bbakersmith/hl3-headwater/src/headwater_state.c

#include "stdint.h"
#include <stdio.h>

#include "headwater_state.h"

void headwater_state_update_samples_per_beat(
  HeadwaterStateChannel *channel,
  uint16_t samples_per_beat
) {
  if(channel->multiplier == 0)
    return;

  uint8_t multiplier = channel->multiplier;
  uint16_t base_samples = samples_per_beat / multiplier;
  uint8_t remainder = samples_per_beat % multiplier;
  uint16_t multiplier_100 = multiplier * 100;

  uint16_t no_remainder_frequency;
  uint16_t remainder_frequency;
  if(remainder != 0) {
    no_remainder_frequency = multiplier_100 / (multiplier - remainder);
    remainder_frequency = multiplier_100 / remainder;
  } else {
    no_remainder_frequency = 0;
    remainder_frequency = 1;
  }

  channel->samples_per_beat = base_samples;
  channel->samples_per_beat_with_remainder = base_samples;

  channel->remainder_frequency = remainder_frequency;
  channel->remainder_priority = remainder_frequency;

  channel->no_remainder_frequency = no_remainder_frequency;
  channel->no_remainder_priority = no_remainder_frequency;
}

HeadwaterStateChannel headwater_state_channel_new(uint16_t samples_per_beat) {
  HeadwaterStateChannel channel = {
    .samples = 0,
    .beats = 0,
    .multiplier = 1,
    .output = 0
  };
  headwater_state_update_samples_per_beat(&channel, samples_per_beat);
  return channel;
}

HeadwaterState headwater_state_new(void) {
  uint32_t samples_per_second = 1000;

  uint16_t samples_per_beat = headwater_state_bpm_to_samples(
    samples_per_second,
    HEADWATER_STATE_DEFAULT_BPM
  );

  HeadwaterStateChannel bpm_channel =
    headwater_state_channel_new(samples_per_beat);

  HeadwaterStateChannel multiplier_a_channel =
    headwater_state_channel_new(samples_per_beat);

  HeadwaterStateChannel multiplier_b_channel =
    headwater_state_channel_new(samples_per_beat);

  HeadwaterStateChannel midi_channel =
    headwater_state_channel_new(samples_per_beat);

  midi_channel.multiplier = 24;
  headwater_state_update_samples_per_beat(&midi_channel, samples_per_beat);

  HeadwaterState state = {
    .bpm = HEADWATER_STATE_DEFAULT_BPM,
    .bpm_channel = bpm_channel,
    .mode = HEADWATER_STATE_MODE_INTERNAL,
    .multiplier_a_channel = multiplier_a_channel,
    .multiplier_b_channel = multiplier_b_channel,
    .midi_channel = midi_channel,
    .output_enabled = 0,
    .preset = 0,
    .reset_count = 0,
    .samples_per_second = samples_per_second,
    .samples_since_reset_count = 0
  };
  return state;
}

uint16_t headwater_state_samples_to_bpm(
  uint32_t samples_per_second,
  uint16_t samples_per_beat
) {
  return (samples_per_second * SECONDS_IN_MINUTE * 10) / samples_per_beat;
}

uint16_t headwater_state_bpm_to_samples(
  uint32_t samples_per_second,
  uint16_t bpm
) {
  return (samples_per_second * SECONDS_IN_MINUTE * 10) / bpm;
}

void headwater_state_stop(HeadwaterState *state) {
  state->output_enabled = 0;
  state->reset_count = 0;
  (state->midi)->writer(MIDI_STOP);
}

void headwater_state_reset_channel(HeadwaterStateChannel *channel) {
  channel->beats = 0;
  channel->samples = 0;
  channel->samples_per_beat_with_remainder = channel->samples_per_beat;
}

void headwater_state_play(HeadwaterState *state) {
  uint8_t previous_output_enabled = state->output_enabled;

  headwater_state_reset_channel(&state->bpm_channel);
  headwater_state_reset_channel(&state->multiplier_a_channel);
  headwater_state_reset_channel(&state->multiplier_b_channel);
  headwater_state_reset_channel(&state->midi_channel);

  state->reset_count++;

  switch(state->mode) {
    case HEADWATER_STATE_MODE_EXTERNAL:
    case HEADWATER_STATE_MODE_TAP:
      if(state->reset_count == 1) {
        // TODO display unknown ---.- ???.?
      } else {
        state->output_enabled = 1;

        state->bpm_channel.samples_per_beat =
          state->samples_since_reset_count;

        state->change_flags |= (1 << HEADWATER_STATE_CHANGE_BPM);
      }
      state->samples_since_reset_count = 0;
      break;
    default:
      state->output_enabled = 1;
      break;
  }

  if(state->output_enabled) {
    if(previous_output_enabled == 0) {
      (state->midi)->writer(MIDI_START);
    } else {
      (state->midi)->writer(MIDI_CONTINUE);
    }
  }
}

void headwater_state_channel_fire(
  HeadwaterStateChannel *channel
) {
  channel->samples_per_beat_with_remainder = channel->samples_per_beat;

  if(channel->remainder_priority < channel->no_remainder_priority) {
    channel->samples_per_beat_with_remainder++;
    channel->remainder_priority += channel->remainder_frequency;
  } else {
    channel->no_remainder_priority += channel->no_remainder_frequency;
  }

  // TODO prevent priority overflow (write test first)

  channel->beats++;
  channel->output = 1;
}

void headwater_state_channel_update_output(
  HeadwaterStateChannel *channel
) {
  if(
    channel->multiplier != 0
    && channel->beats < channel->multiplier
    && channel->samples == 0
  ) {
    headwater_state_channel_fire(channel);
  } else {
    channel->output = 0;
  }
}

void headwater_state_channel_reset(
  HeadwaterStateChannel *channel
) {
  channel->beats = 0;
  channel->samples = 0;
  channel->no_remainder_priority = channel->no_remainder_frequency;
  channel->remainder_priority = channel->remainder_frequency;
}

void headwater_state_update_outputs(HeadwaterState *state) {
  headwater_state_channel_update_output(&state->bpm_channel);

  if(state->bpm_channel.output == 1) {
    headwater_state_channel_reset(&state->multiplier_a_channel);
    headwater_state_channel_reset(&state->multiplier_b_channel);
    headwater_state_channel_reset(&state->midi_channel);
  }

  headwater_state_channel_update_output(&state->multiplier_a_channel);
  headwater_state_channel_update_output(&state->multiplier_b_channel);
  headwater_state_channel_update_output(&state->midi_channel);
}

void headwater_state_channel_increment_counts(
  HeadwaterStateChannel *channel
) {
  if(channel->samples < UINT16_MAX)
    channel->samples++;

  if(channel->beats < channel->multiplier) {
    if(channel->samples_per_beat_with_remainder <= channel->samples) {
      channel->samples = 0;
    }
  }
}

void headwater_state_increment_counts(HeadwaterState *state) {
  headwater_state_channel_increment_counts(&state->bpm_channel);
  headwater_state_channel_increment_counts(&state->multiplier_a_channel);
  headwater_state_channel_increment_counts(&state->multiplier_b_channel);
  headwater_state_channel_increment_counts(&state->midi_channel);

  // timeout & reset
  if(state->samples_since_reset_count < UINT16_MAX) {
    state->samples_since_reset_count++;
  } else {
    state->reset_count = 0;
    state->samples_since_reset_count = 0;
  }

  // loop based on internal clock for internal and tap modes
  switch(state->mode) {
    case HEADWATER_STATE_MODE_INTERNAL:
    case HEADWATER_STATE_MODE_TAP:
      state->bpm_channel.beats = 0;
      break;
    default:
      break;
  }
}

void headwater_state_cycle(HeadwaterState *state) {
  if(state->output_enabled == 1) {
    headwater_state_update_outputs(state);
  } else {
    state->bpm_channel.output = 0;
    state->multiplier_a_channel.output = 0;
    state->multiplier_b_channel.output = 0;
    state->midi_channel.output = 0;
  }

  if(state->bpm_channel.output == 1)
    headwater_state_handle_change_after_beat(state);

  headwater_state_increment_counts(state);
}

bool headwater_state_has_change_now(uint8_t change_flags) {
  uint8_t mask =
    (1 << HEADWATER_STATE_CHANGE_STOP)
    | (1 << HEADWATER_STATE_CHANGE_PLAY)
    | (1 << HEADWATER_STATE_CHANGE_MODE);

  return (mask & change_flags) != 0;
}

void headwater_state_handle_change_now(HeadwaterState *state) {
  uint8_t change_flags = state->change_flags;
  if(!headwater_state_has_change_now(change_flags))
    return;

  if((change_flags & (1 << HEADWATER_STATE_CHANGE_PLAY))) {
    state->change_flags &= ~(1 << HEADWATER_STATE_CHANGE_PLAY);
    headwater_state_play(state);

  } else if((change_flags & (1 << HEADWATER_STATE_CHANGE_STOP))) {
    state->change_flags &= ~(1 << HEADWATER_STATE_CHANGE_STOP);
    headwater_state_stop(state);

  } else if((change_flags & (1 << HEADWATER_STATE_CHANGE_MODE))) {
    state->change_flags &= ~(1 << HEADWATER_STATE_CHANGE_MODE);
    // react to mode change here, if ever a reason to
  }
}

bool headwater_state_has_change_after_beat(uint8_t change_flags) {
  uint8_t mask =
    (1 << HEADWATER_STATE_CHANGE_BPM)
    | (1 << HEADWATER_STATE_CHANGE_MULTIPLIER_A)
    | (1 << HEADWATER_STATE_CHANGE_MULTIPLIER_B);

  return (mask & change_flags) != 0;
}

void headwater_state_handle_change_after_beat(HeadwaterState *state) {
  uint8_t change_flags = state->change_flags;
  if(!headwater_state_has_change_after_beat(change_flags))
    return;

  if((change_flags & (1 << HEADWATER_STATE_CHANGE_BPM))) {
    state->change_flags &= ~(1 << HEADWATER_STATE_CHANGE_BPM);
    state->change_flags &= ~(1 << HEADWATER_STATE_CHANGE_MULTIPLIER_A);
    state->change_flags &= ~(1 << HEADWATER_STATE_CHANGE_MULTIPLIER_B);

    switch(state->mode) {
      case HEADWATER_STATE_MODE_INTERNAL:
        headwater_state_update_samples_per_beat(
          &state->bpm_channel,
          headwater_state_bpm_to_samples(
            state->samples_per_second,
            state->bpm
          )
        );
        break;

      case HEADWATER_STATE_MODE_EXTERNAL:
      case HEADWATER_STATE_MODE_TAP:
        state->bpm = headwater_state_samples_to_bpm(
          state->samples_per_second,
          state->bpm_channel.samples_per_beat
        );
        break;

      default:
        break;
    }

    headwater_state_update_samples_per_beat(
      &state->multiplier_a_channel,
      state->bpm_channel.samples_per_beat
    );

    headwater_state_update_samples_per_beat(
      &state->multiplier_b_channel,
      state->bpm_channel.samples_per_beat
    );

    headwater_state_update_samples_per_beat(
      &state->midi_channel,
      state->bpm_channel.samples_per_beat
    );

  }

  if((change_flags & (1 << HEADWATER_STATE_CHANGE_MULTIPLIER_A))) {
    state->change_flags &= ~(1 << HEADWATER_STATE_CHANGE_MULTIPLIER_A);
    headwater_state_update_samples_per_beat(
      &state->multiplier_a_channel,
      state->bpm_channel.samples_per_beat
    );

  }

  if((change_flags & (1 << HEADWATER_STATE_CHANGE_MULTIPLIER_B))) {
    state->change_flags &= ~(1 << HEADWATER_STATE_CHANGE_MULTIPLIER_B);
    headwater_state_update_samples_per_beat(
      &state->multiplier_b_channel,
      state->bpm_channel.samples_per_beat
    );
  }
}
