bbakersmith/hl3-headwater/src/headwater.c

#include "stdint.h"
#include "headwater.h"


static int8_t CLOCK_EXT_MODE_SYNC = 0;
static int8_t CLOCK_EXT_MODE_TAP = 1;
static int8_t CLOCK_EXT_MODE_EXT = 2;
static int8_t CLOCK_EXT_MODE_CV = 3;


static int8_t CLOCK_RUNNING_STOP = 0;
static int8_t CLOCK_RUNNING_PLAY = 1;


static uint16_t BPM_MIN = 10;
static uint16_t BPM_MAX = 3000;


static uint8_t MIN_MULTIPLIER = 1;
static uint8_t MAX_MULTIPLIER = 99;


static uint8_t SECONDS_IN_MINUTE = 60;
static uint32_t SAMPLES_PER_SECOND = 1000;


static int8_t CLOCK_STATE_DEFAULT_EXT_MODE = 0;
static int16_t CLOCK_STATE_DEFAULT_TBPM = 1200;
static int8_t CLOCK_STATE_DEFAULT_MULTIPLIER = 1;
static int8_t CLOCK_STATE_DEFAULT_RUNNING = 0;
static uint16_t CLOCK_STATE_DEFAULT_SAMPLES_PER_OUTPUT = 500;
static uint16_t CLOCK_STATE_DEFAULT_SAMPLES_PER_MULTIPLIED = 500;
static uint16_t CLOCK_STATE_DEFAULT_SAMPLE_COUNT = 0;
static uint16_t CLOCK_STATE_DEFAULT_MULTIPLIED_SAMPLE_COUNT = 0;
static uint16_t CLOCK_STATE_DEFAULT_MULTIPLIED_COUNT = 0;


int8_t rotary_encoder_modifier(int8_t b_value) {
  if(b_value) {
    return -1;
  } else {
    return 1;
  }
}


int8_t tbpm_encoder_modifier(int8_t b_value, int8_t tenths_button) {
  int8_t modifier = rotary_encoder_modifier(b_value);

  // TODO this might be backwards
  if(tenths_button == 0) {
    modifier *= 10;
  }

  return modifier;
}


// TODO either switch to unsigned for tbpm and mult or limit to 2bpm
int16_t modify_tbpm(int16_t tbpm, int8_t b_value, int8_t tenths_button) {
  int8_t modifier = tbpm_encoder_modifier(b_value, tenths_button);
  int16_t new_tbpm = tbpm + modifier;

  if(new_tbpm < BPM_MIN) {
    new_tbpm = BPM_MIN;
  } else if(BPM_MAX < new_tbpm) {
    new_tbpm = BPM_MAX;
  }

  return new_tbpm;
}


int8_t modify_multiplier(int8_t multiplier, int8_t b_value) {
  int8_t modifier = rotary_encoder_modifier(b_value);
  int8_t new_multiplier = multiplier + modifier;

  if(new_multiplier < MIN_MULTIPLIER) {
    new_multiplier = MIN_MULTIPLIER;
  } else if(MAX_MULTIPLIER < new_multiplier) {
    new_multiplier = MAX_MULTIPLIER;
  }

  return new_multiplier;
}


// TODO: update LED functions


uint16_t samples_per_output(int16_t tbpm) {
  return (SAMPLES_PER_SECOND * SECONDS_IN_MINUTE * 10) / tbpm;
}


uint16_t samples_per_multiplied(int16_t tbpm, int8_t multiplier) {
  return samples_per_output(tbpm) / multiplier;
}


// TODO take system clock speed? sample rate?
ClockState create_clock_state() {
  ClockState clock_state;
  clock_state.tbpm = CLOCK_STATE_DEFAULT_TBPM;
  clock_state.multiplier = CLOCK_STATE_DEFAULT_MULTIPLIER;
  clock_state.running = CLOCK_STATE_DEFAULT_RUNNING;
  clock_state.samples_per_output = CLOCK_STATE_DEFAULT_SAMPLES_PER_OUTPUT;
  clock_state.samples_per_multiplied = CLOCK_STATE_DEFAULT_SAMPLES_PER_MULTIPLIED;
  clock_state.sample_count = CLOCK_STATE_DEFAULT_SAMPLE_COUNT;
  clock_state.multiplied_sample_count = CLOCK_STATE_DEFAULT_MULTIPLIED_SAMPLE_COUNT;
  clock_state.multiplied_count = CLOCK_STATE_DEFAULT_MULTIPLIED_COUNT;
  return clock_state;
}


void update_clock_config(ClockState *clock_state, int16_t tbpm, int8_t multiplier) {
  clock_state->tbpm = tbpm;
  clock_state->multiplier = multiplier;
  clock_state->samples_per_output = samples_per_output(tbpm);
  clock_state->samples_per_multiplied = samples_per_multiplied(tbpm, multiplier);
}


void stop_clock(ClockState *clock_state) {
  clock_state->running = CLOCK_RUNNING_STOP;
}


void start_clock(ClockState *clock_state) {
  clock_state->running = CLOCK_RUNNING_PLAY;
  clock_state->sample_count = 0;
  clock_state->multiplied_count = 0;
}


void increment_clock(ClockState *clock_state) {
  clock_state->sample_count += 1;
  clock_state->multiplied_sample_count += 1;
  // TODO move this into update clock outputs to reduce branching?
  if(clock_state->samples_per_output <= clock_state->sample_count) {
    clock_state->sample_count = 0;
    clock_state->multiplied_sample_count = 0;
    clock_state->multiplied_count = 0;
  }
}


void update_clock_outputs(ClockState *clock_state, UpdateOutputFn output_fn, UpdateOutputFn multiplied_fn) {
  if(clock_state->sample_count == 0) {
    output_fn(1);
    multiplied_fn(1);
    clock_state->multiplied_count += 1;
  } else {
    output_fn(0);
    if(clock_state->multiplied_count < clock_state->multiplier &&
        clock_state->samples_per_multiplied <= clock_state->multiplied_sample_count) {

      clock_state->multiplied_count += 1;
      clock_state->multiplied_sample_count = 0;
      multiplied_fn(1);
    } else {
      multiplied_fn(0);
    }
  }
}


void cycle_clock(ClockState *clock_state, UpdateOutputFn output_fn, UpdateOutputFn multiplied_fn) {
  // TODO handle this at the interrupt level?
  // ex. play button enables TIMER1_COMPA interrupt, stop disables it
  if(clock_state->running == CLOCK_RUNNING_PLAY) {
    update_clock_outputs(clock_state, output_fn, multiplied_fn);
    increment_clock(clock_state);
  }
}
