bbakersmith/hl3-headwater/test/run_tests.c

#include "unity_fixture.h"

static void run_all_tests(void)
{
  RUN_TEST_GROUP(api);
  RUN_TEST_GROUP(bytes);
  RUN_TEST_GROUP(debounce);
  RUN_TEST_GROUP(lcd);
  RUN_TEST_GROUP(midi);
  RUN_TEST_GROUP(queue);
  RUN_TEST_GROUP(ui);
  RUN_TEST_GROUP(headwater_api);
  RUN_TEST_GROUP(headwater_state);
  RUN_TEST_GROUP(headwater_ui);
}

int main(int argc, const char * argv[])
{
  return UnityMain(argc, argv, run_all_tests);
}
